dennowiggle/Retro-PETER/Hardware/PETER/output/PETER_V0_3d_Bottom.jpg

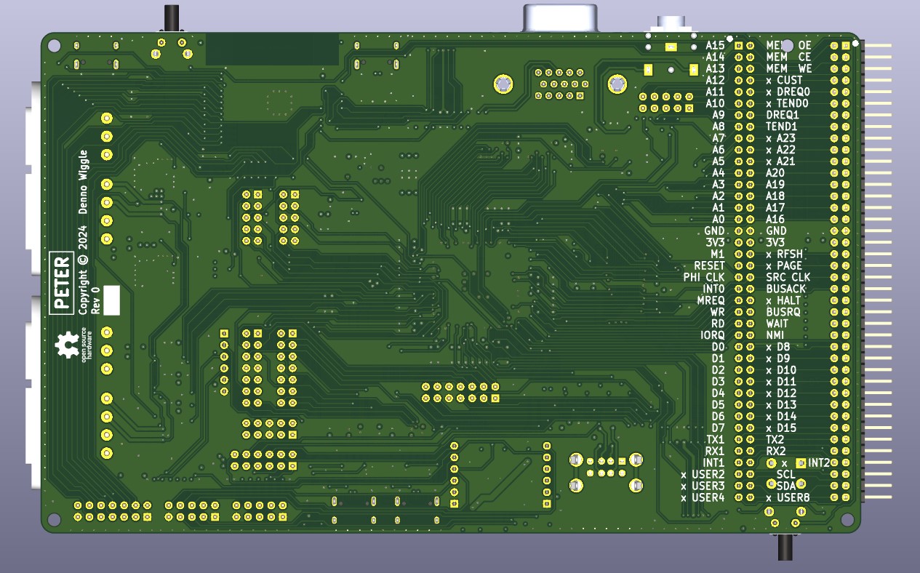
Hardware/PETER/output/PETER_V0_3d_Bottom.jpg
