dennowiggle/Retro-PETER/Hardware/PETER/output/PETER_V0_3d_Front.jpg

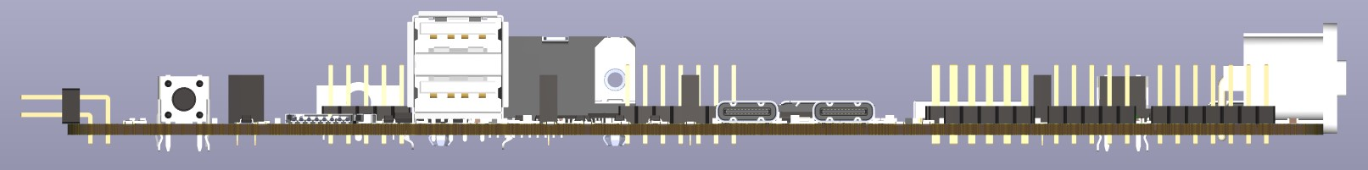
Hardware/PETER/output/PETER_V0_3d_Front.jpg
