dennowiggle/Retro-PETER/Hardware/PETER/output/PETER_V0_3d_Rear.jpg

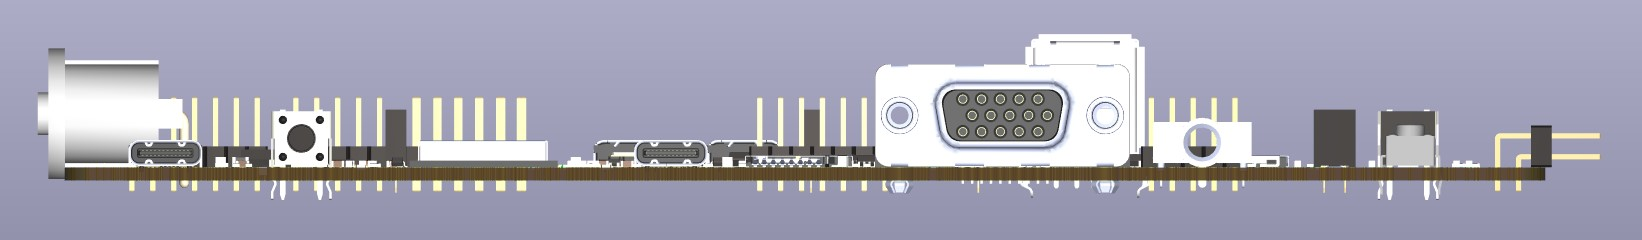
Hardware/PETER/output/PETER_V0_3d_Rear.jpg
