dennowiggle/Retro-PETER/Hardware/BALD/output/BALD_V0.0_BW.pdf

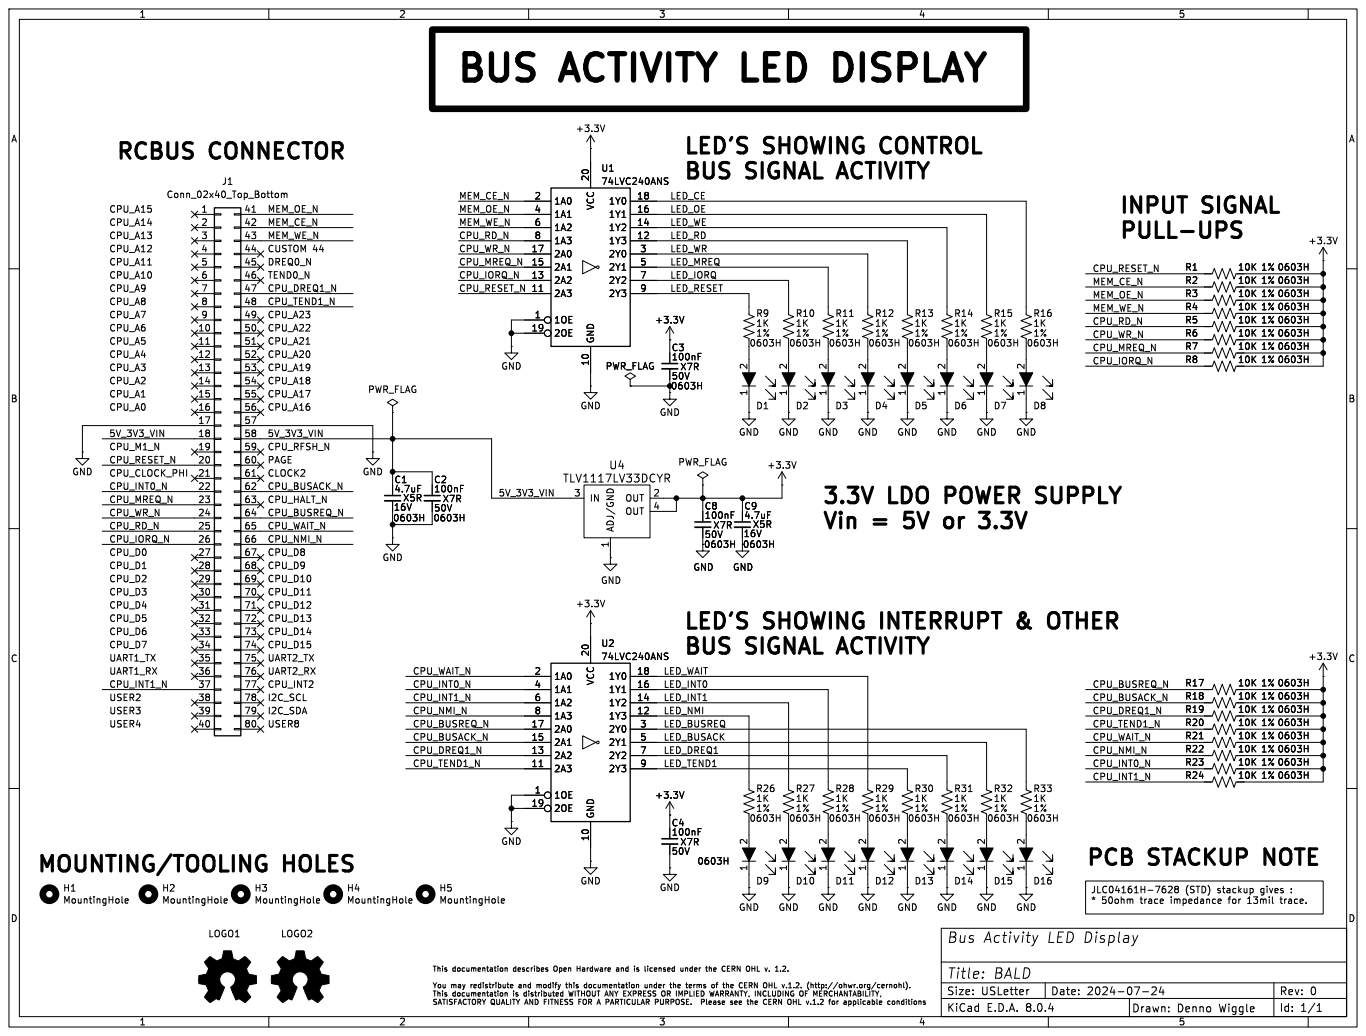
[picture p65: page 1]

Bus Activity LED Display
