dennowiggle/Retro-PETER/Hardware/BALD/output/BALD_V0.0_Color.pdf

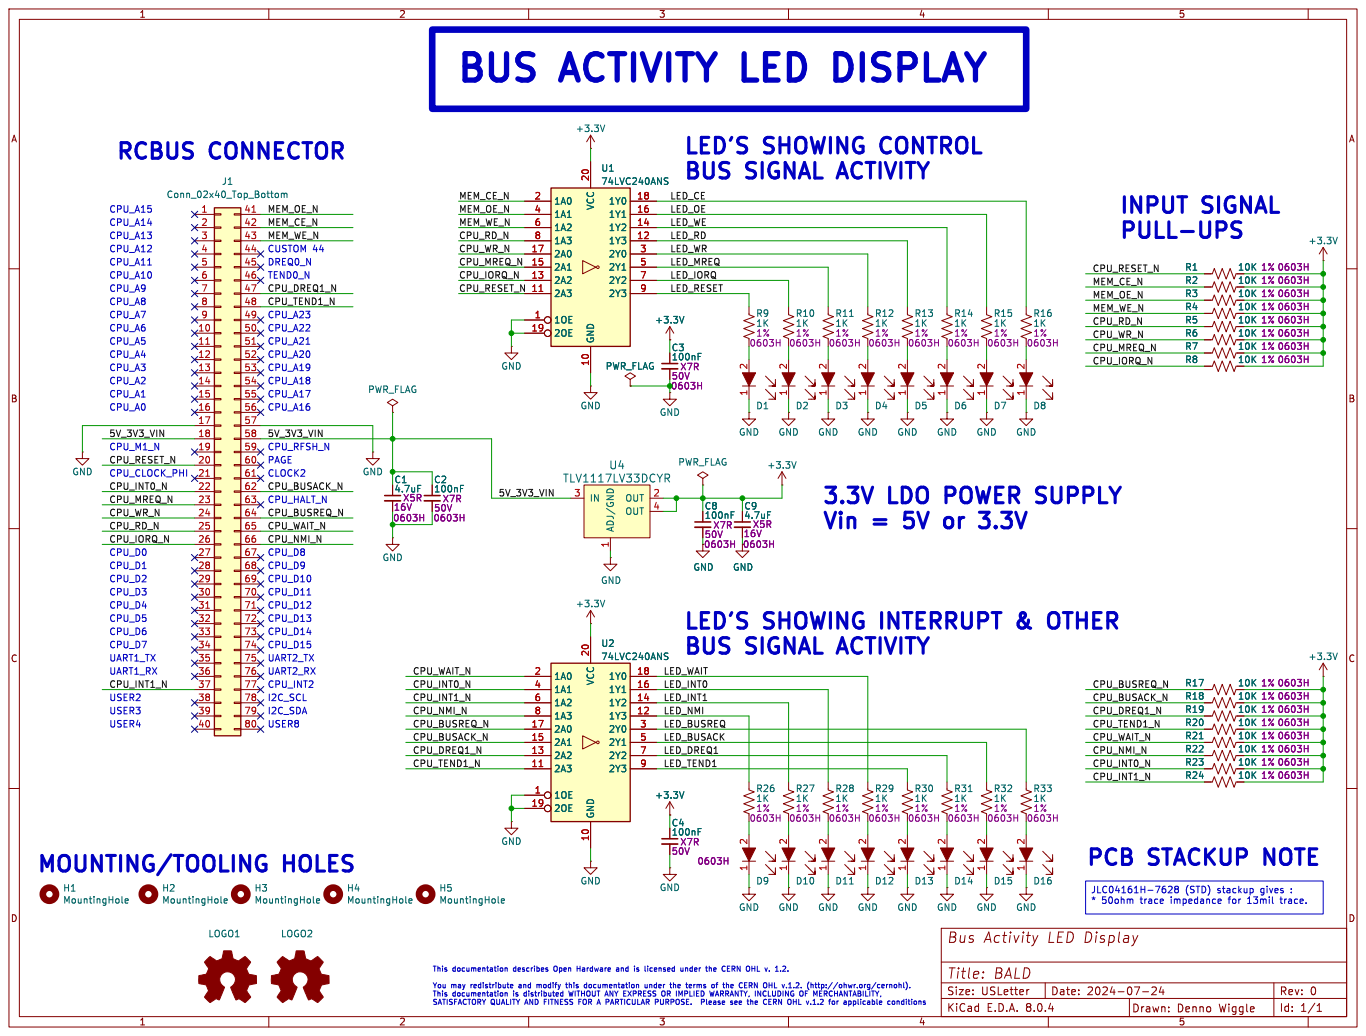
[picture p66: page 1]

Bus Activity LED Display
