dennowiggle/Retro-PETER/Hardware/GOLD/output/GOLD_V0.0_BW.pdf

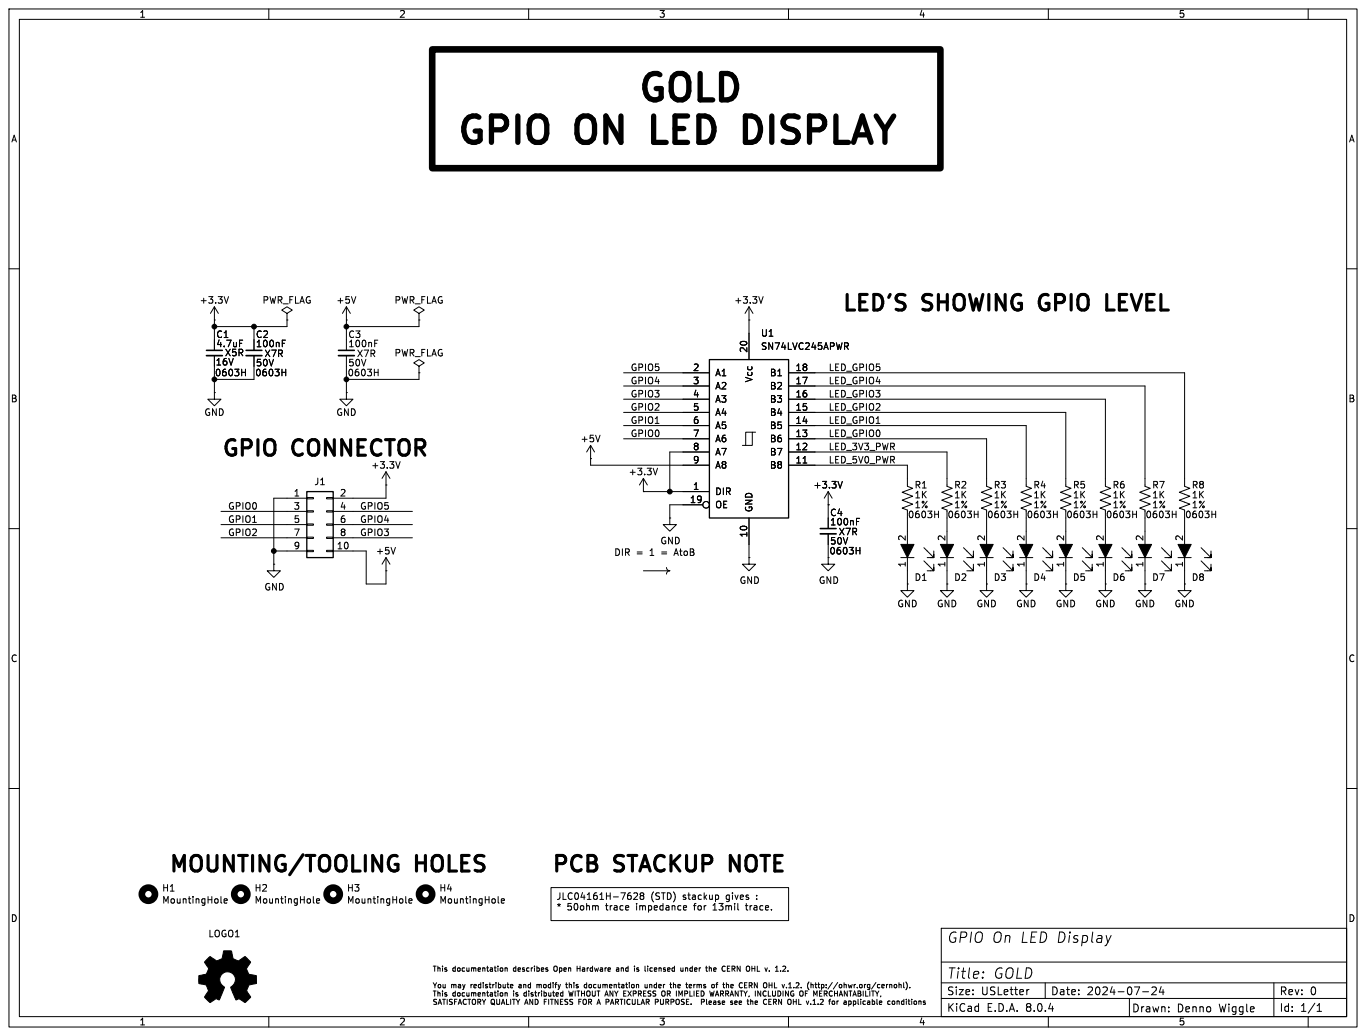
[picture p67: page 1]

GPIO ON LED DISPLAY

GPIO On LED Display
