dennowiggle/Retro-PETER/Hardware/GOLD/output/GOLD_V0.0_Color.pdf

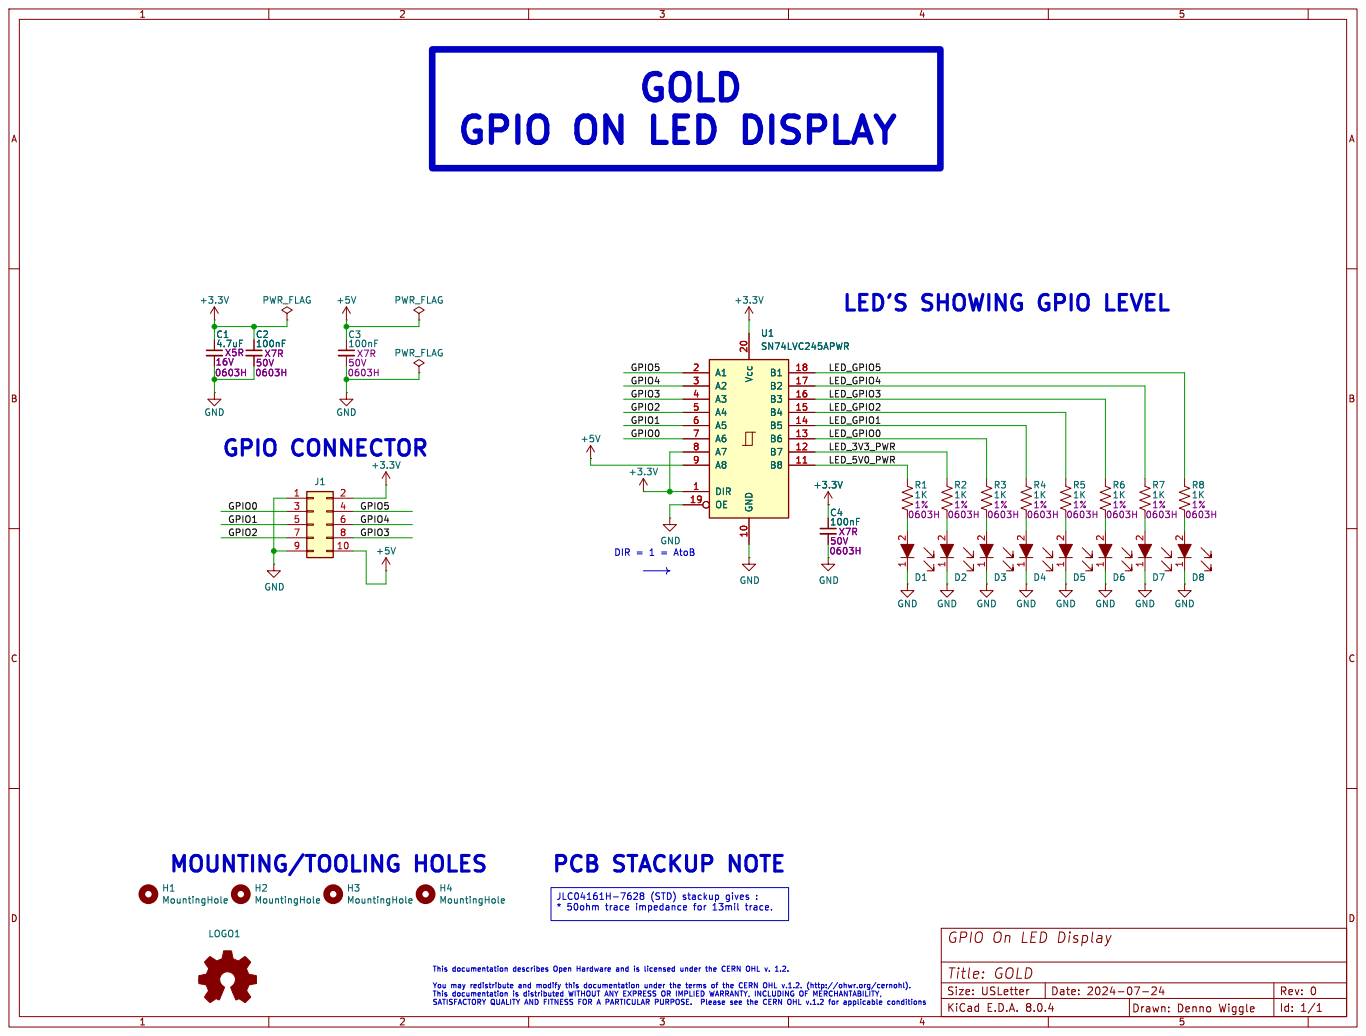
[picture p68: page 1]

GPIO ON LED DISPLAY

LED'S SHOWING GPIO LEVEL

GPIO On LED Display
