dennowiggle/Retro-PETER/Hardware/PETER/output/PETER_V0.0_Color.pdf

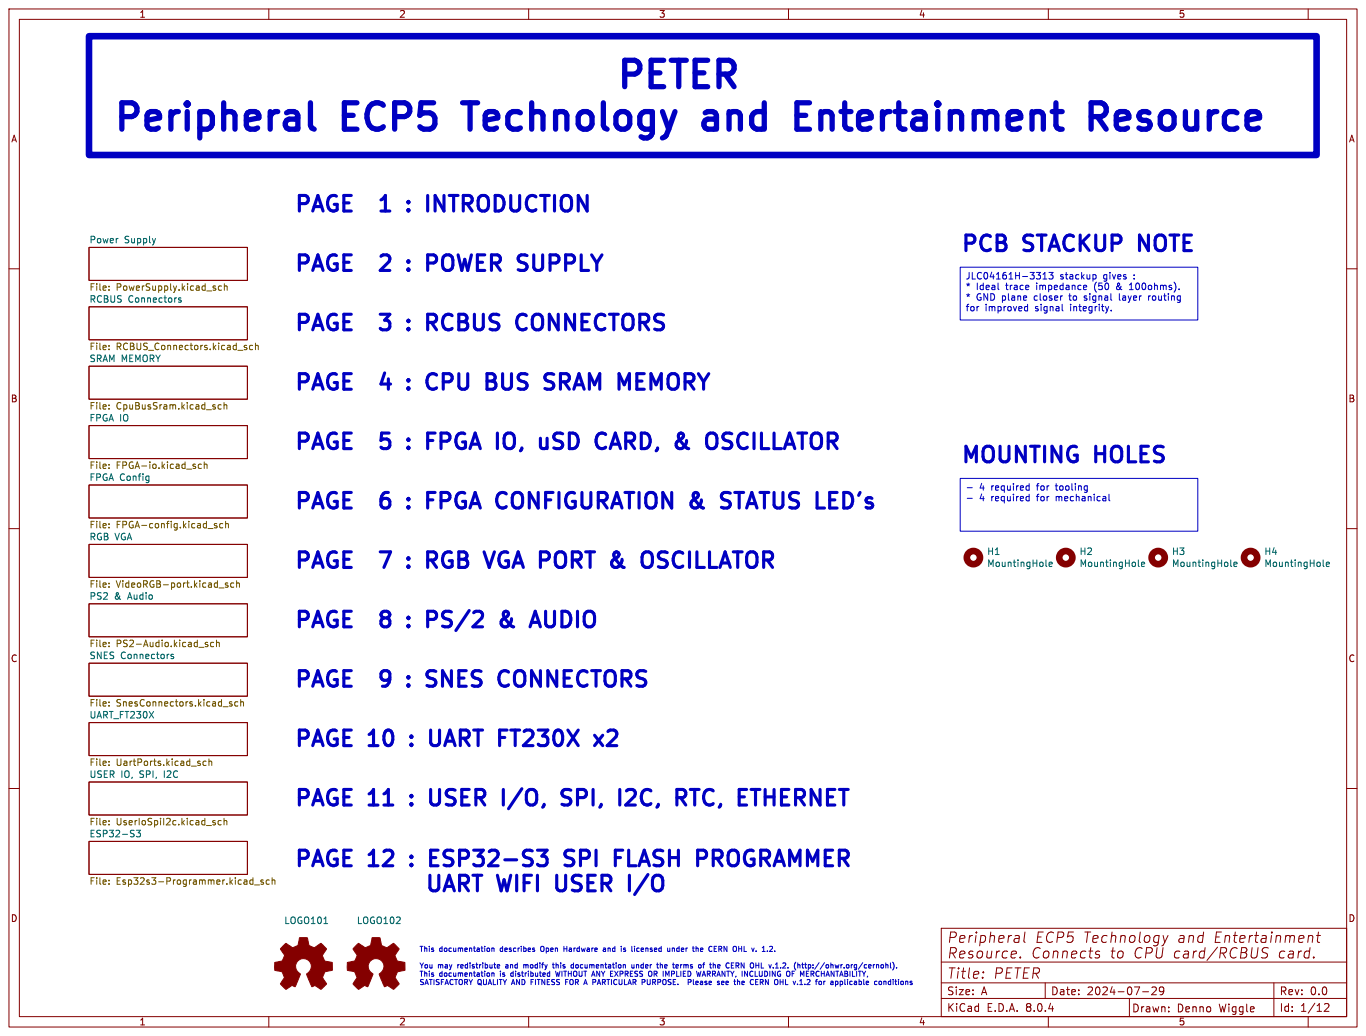
[picture p81: page 1]

Power Supply File: PowerSupply.kicad_sch SRAM MEMORY
File: FPGA-io.kicad_sch PS2 & Audio File: PS2-Audio.kicad_sch FPGA Config File: FPGA-config.kicad_sch SNES Connectors File: SnesConnectors.kicad_sch USER IO, SPI, I2C

RCBUS Connectors File: RCBUS_Connectors.kicad_sch FPGA IO

File: CpuBusSram.kicad_sch RGB VGA

File: UartPorts.kicad_sch ESP32-S3 File: Esp32s3-Programmer.kicad_sch

PAGE 11 : USER I/O, SPI, I2C, RTC, ETHERNET

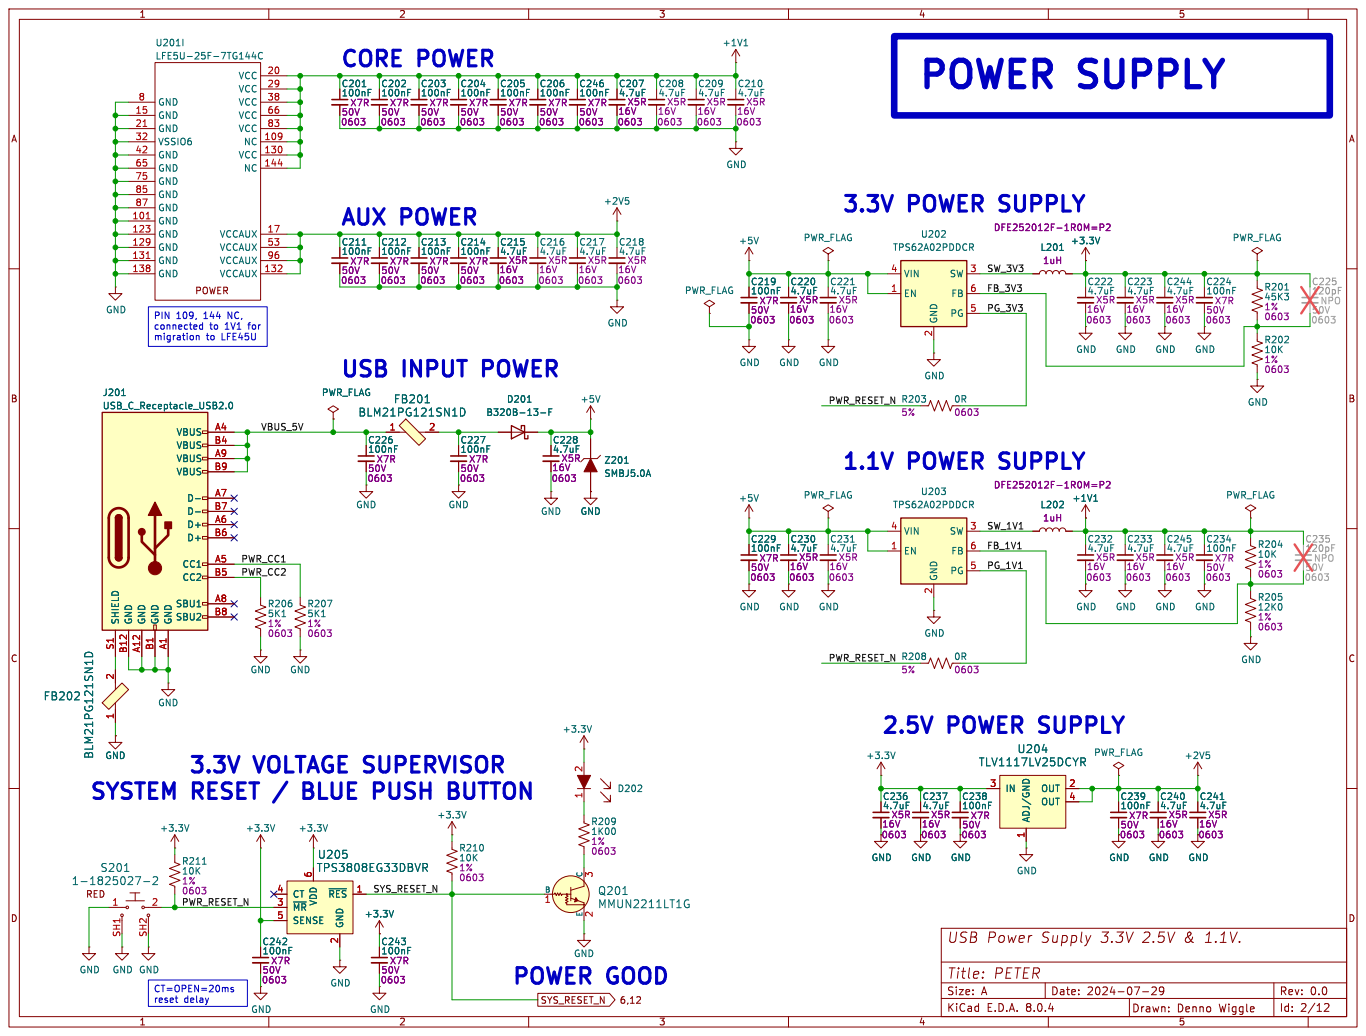
[picture p82: page 2]

2 SW 3 VIN 4 PG 5 FB 6 U202 TPS62A02PDDCR

2 SW 3 VIN 4 PG 5 FB 6 U203 TPS62A02PDDCR GND

1 2 D202 GND GND
SYSTEM RESET / BLUE PUSH BUTTON

2 ~{MR} 3 CT 4 SENSE 5 VDD

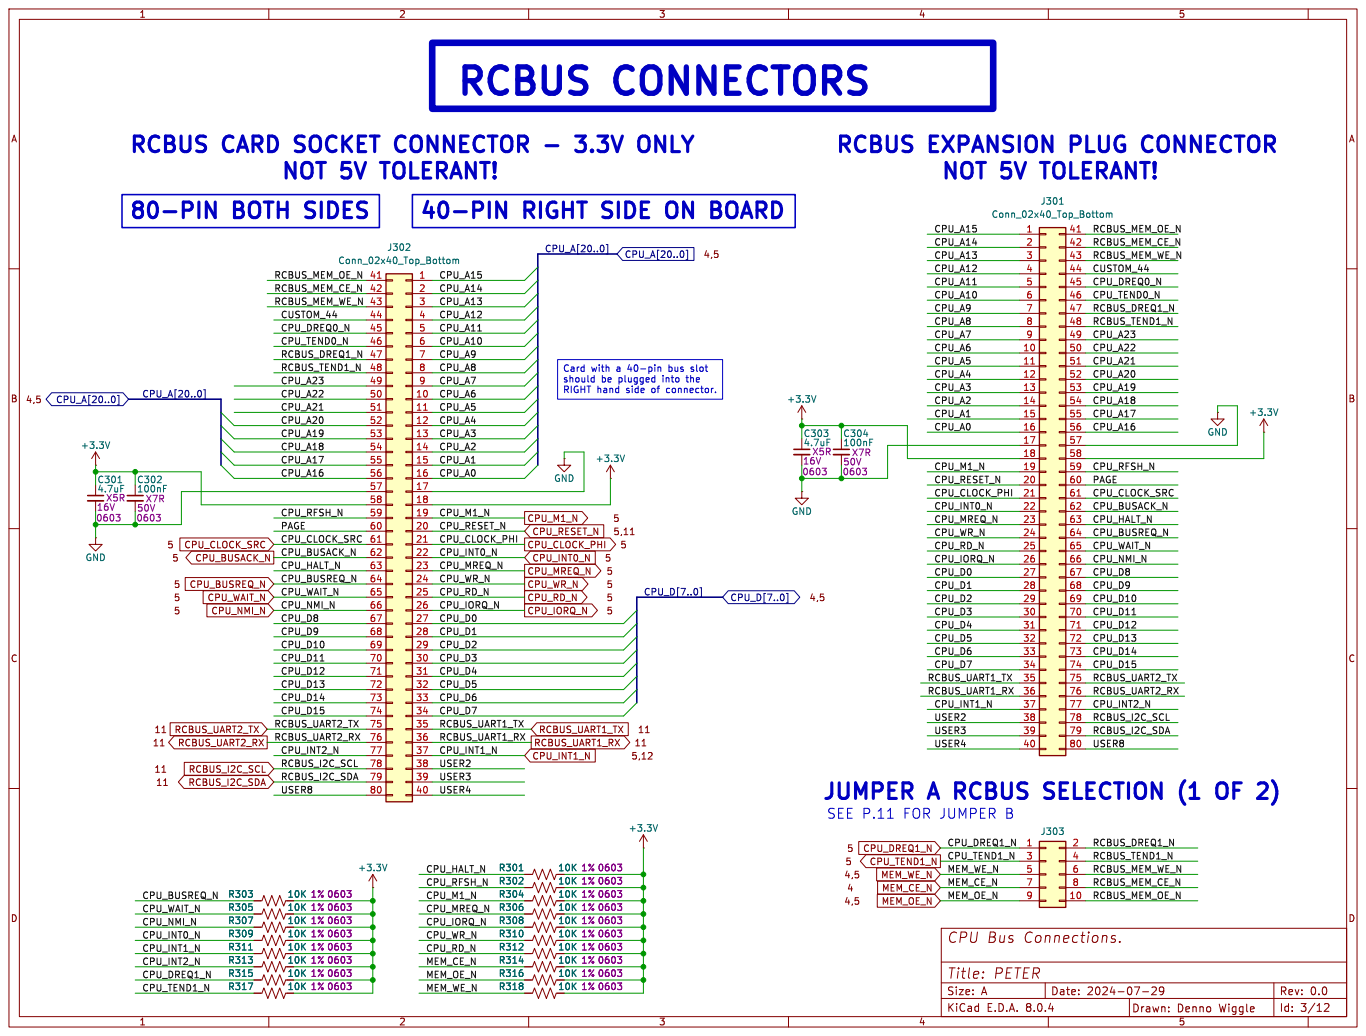
[picture p83: page 3]

RCBUS CARD SOCKET CONNECTOR - 3.3V ONLY

RCBUS EXPANSION PLUG CONNECTOR

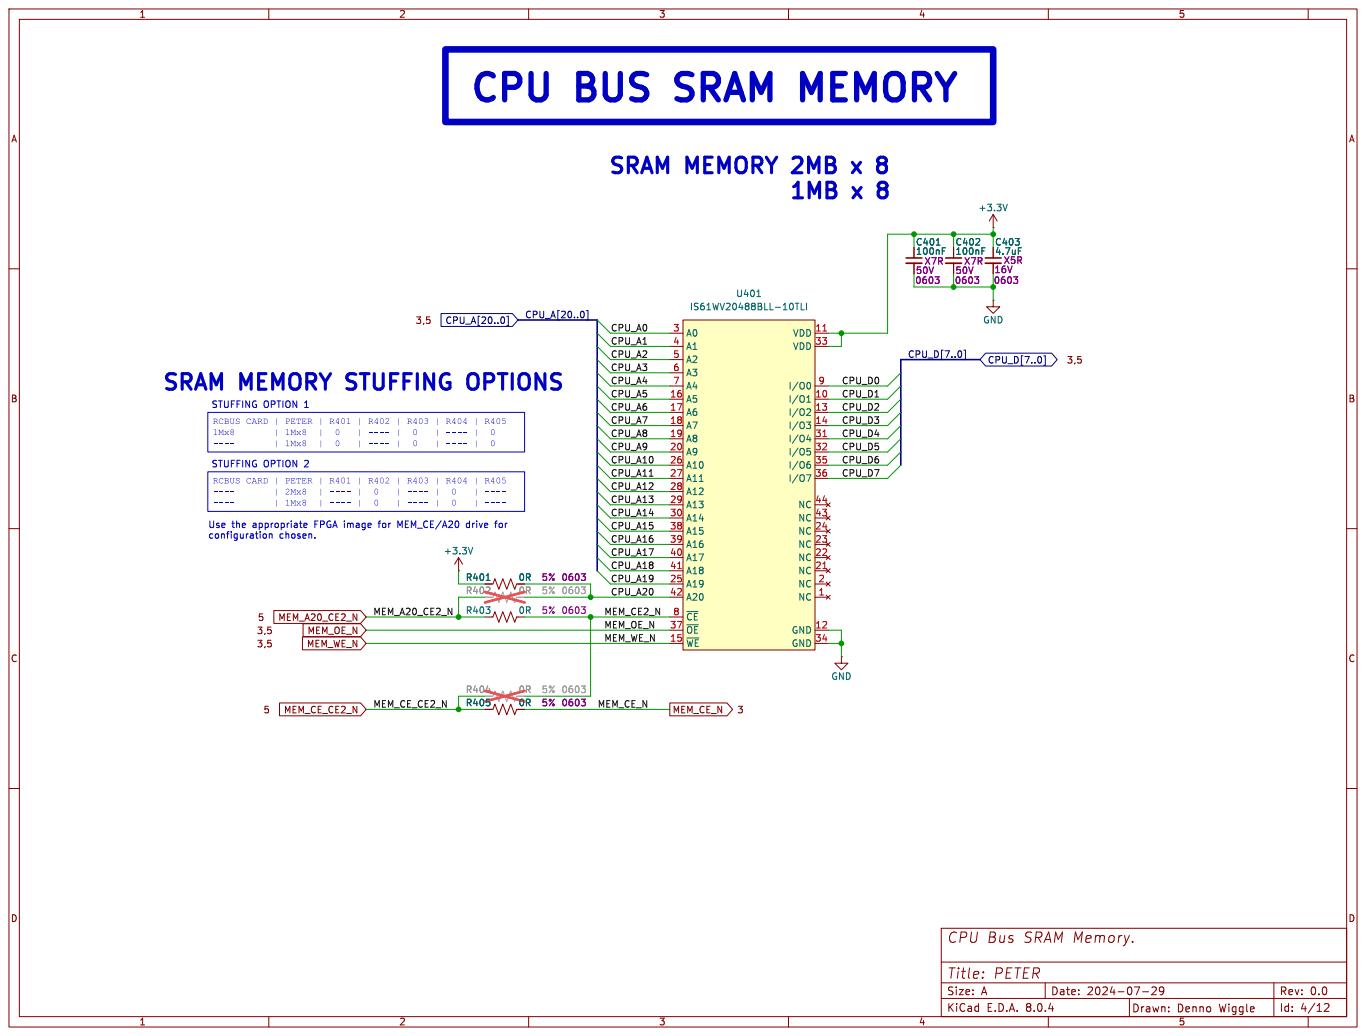
[picture p84: page 4]

CPU BUS SRAM MEMORY

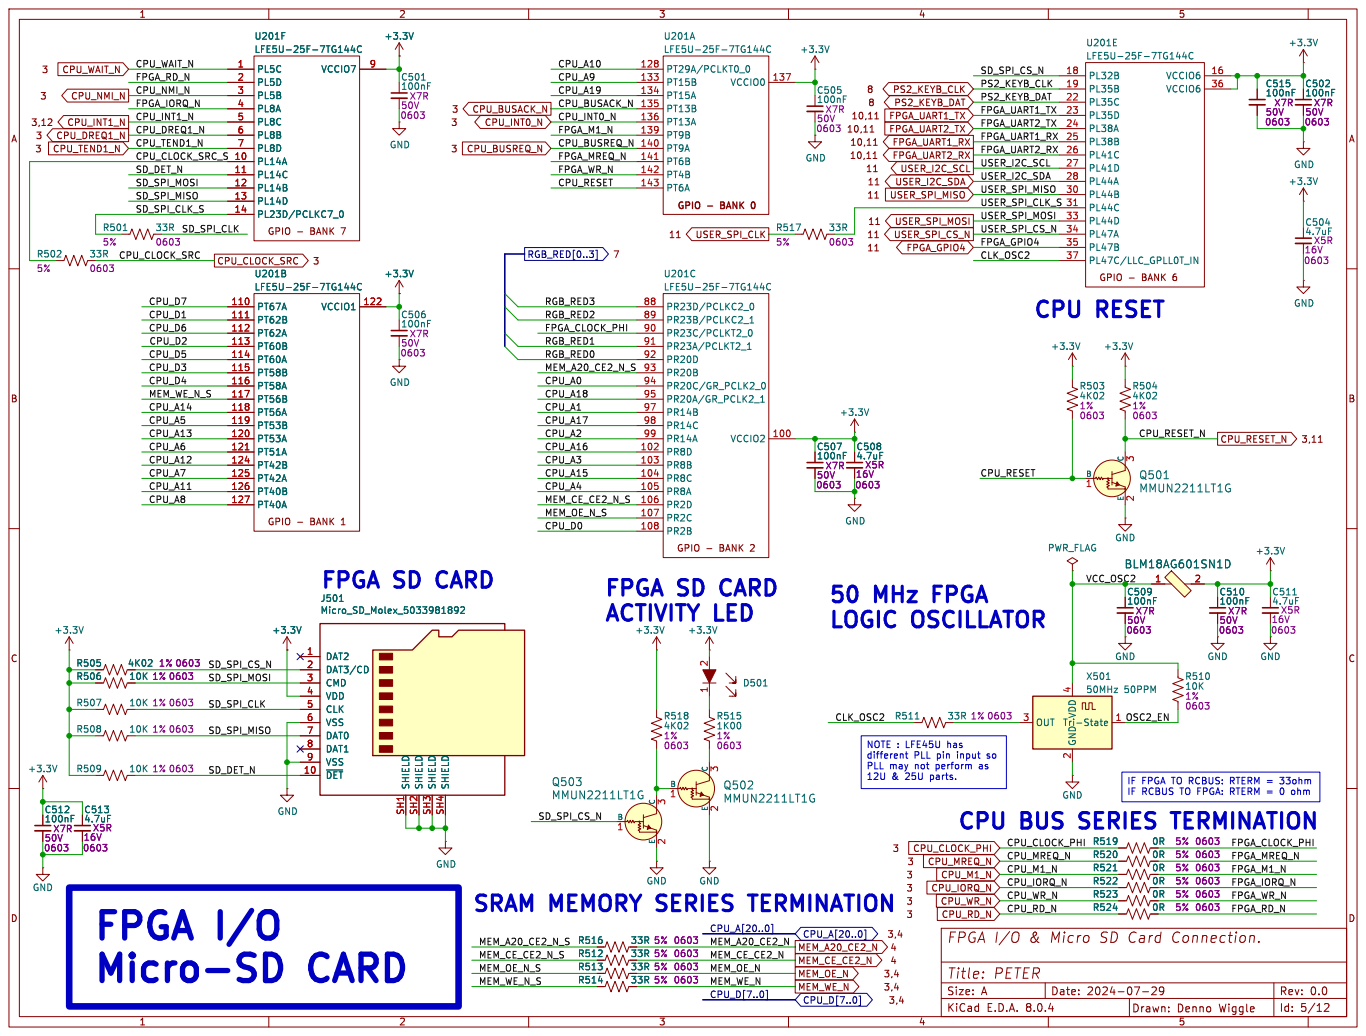
[picture p85: page 5]

IF FPGA TO RCBUS: RTERM = 33ohm

CPU BUS SERIES TERMINATION

GND
SRAM MEMORY SERIES TERMINATION

FPGA I/O & Micro SD Card Connection.

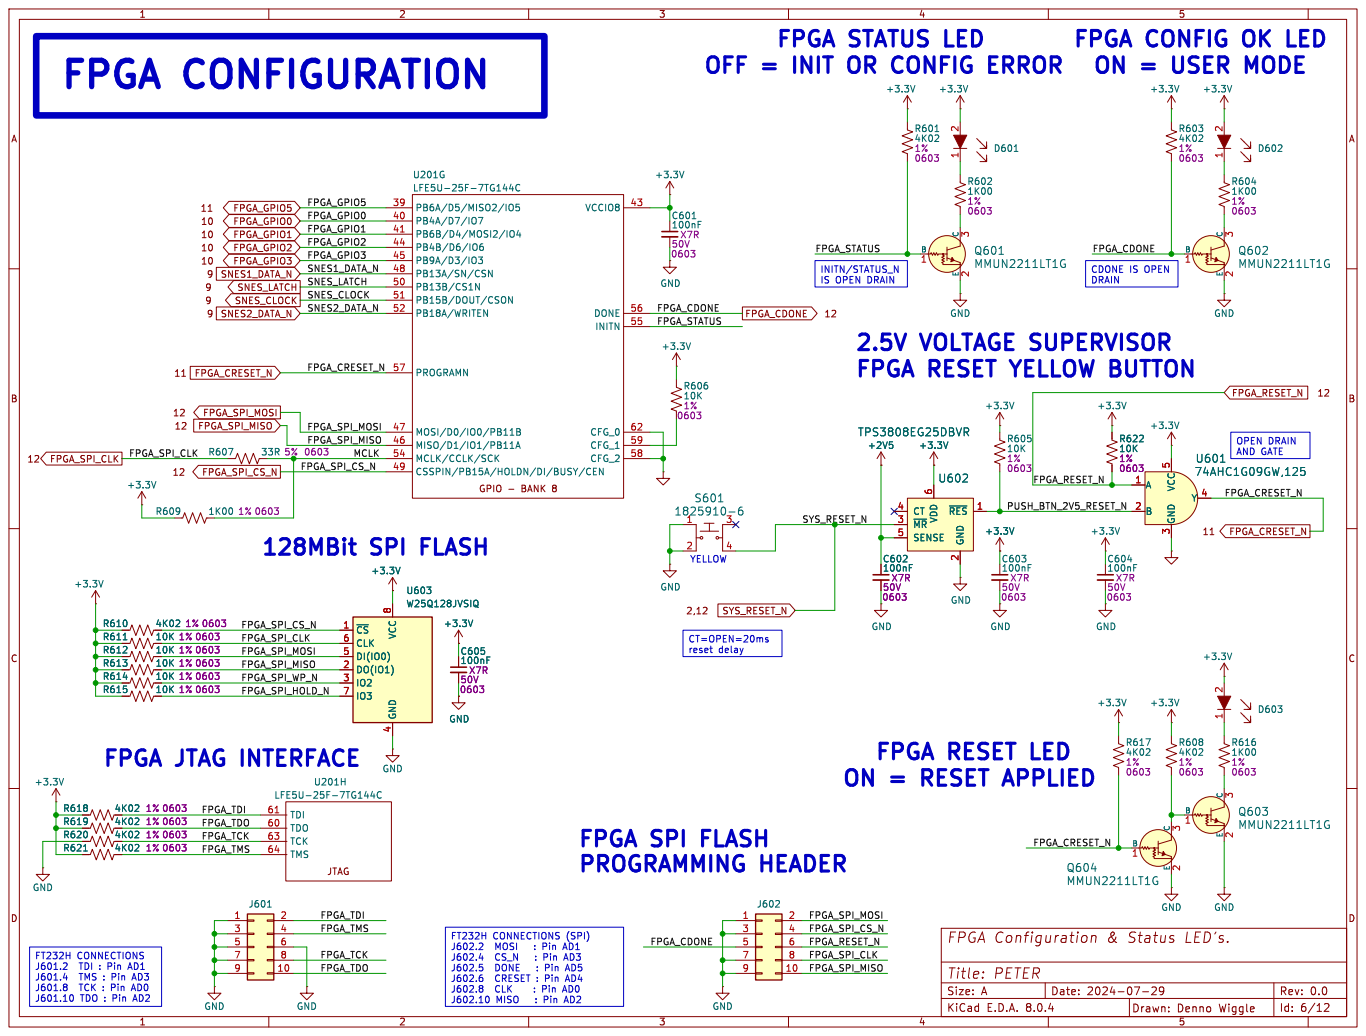
[picture p86: page 6]

FPGA STATUS LED
OFF = INIT OR CONFIG ERROR

AND GATE FPGA CONFIGURATION

2.5V VOLTAGE SUPERVISOR
FPGA RESET YELLOW BUTTON

2 ~{MR} 3 CT 4 SENSE 5 VDD

YELLOW FPGA SPI FLASH

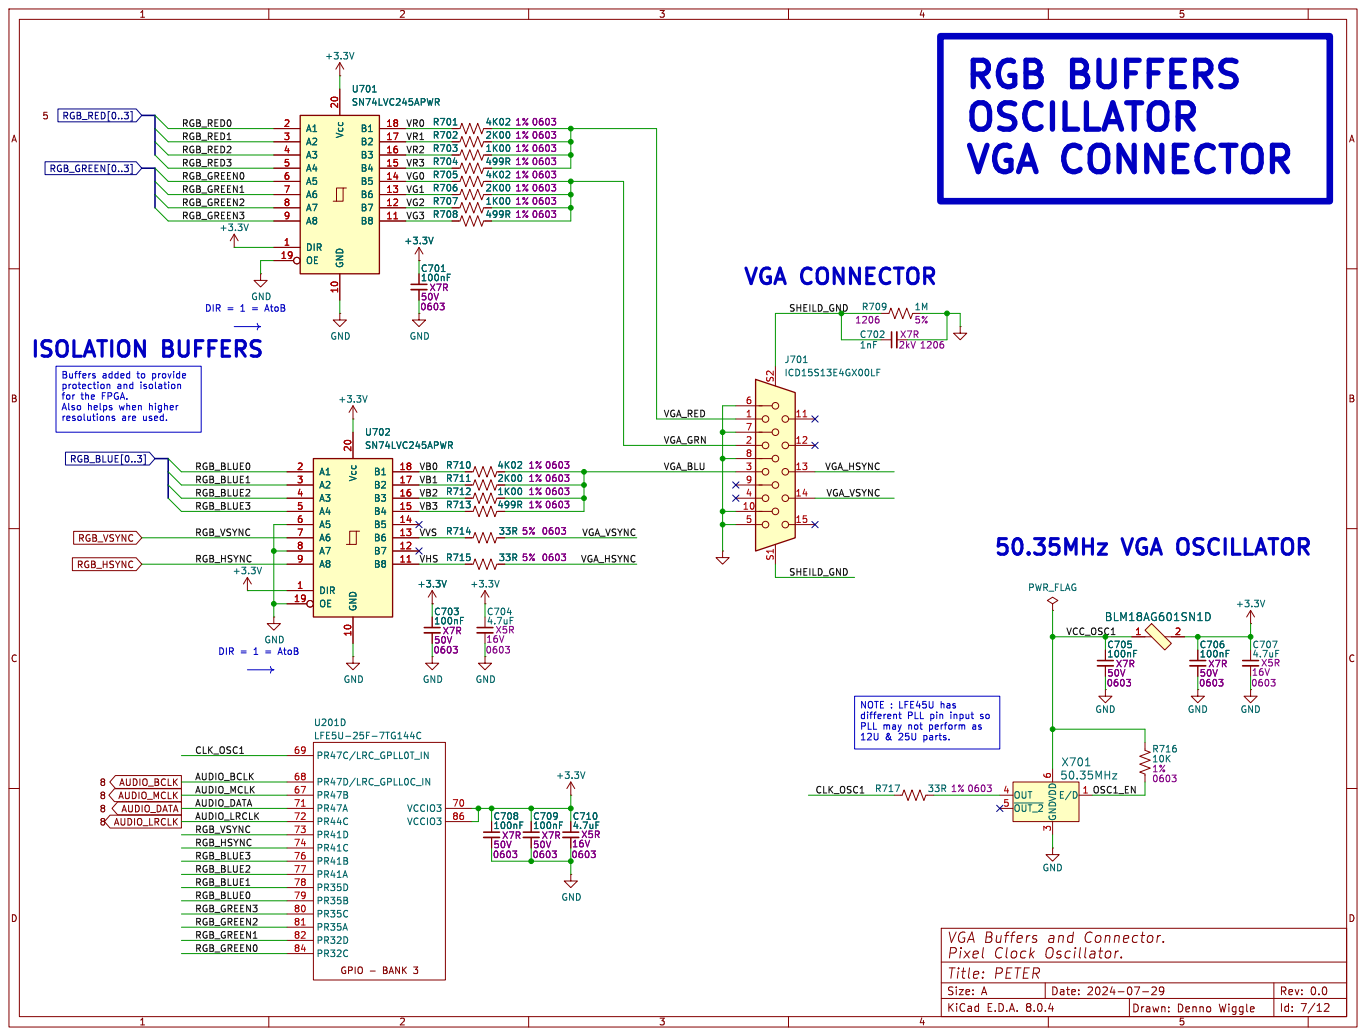
[picture p87: page 7]

Buffers added to provide
for the FPGA. Also helps when higher
8 AUDIO_LRCLK RGB_HSYNC

VGA Buffers and Connector.
Pixel Clock Oscillator.
Id: 7/12 Title: PETER

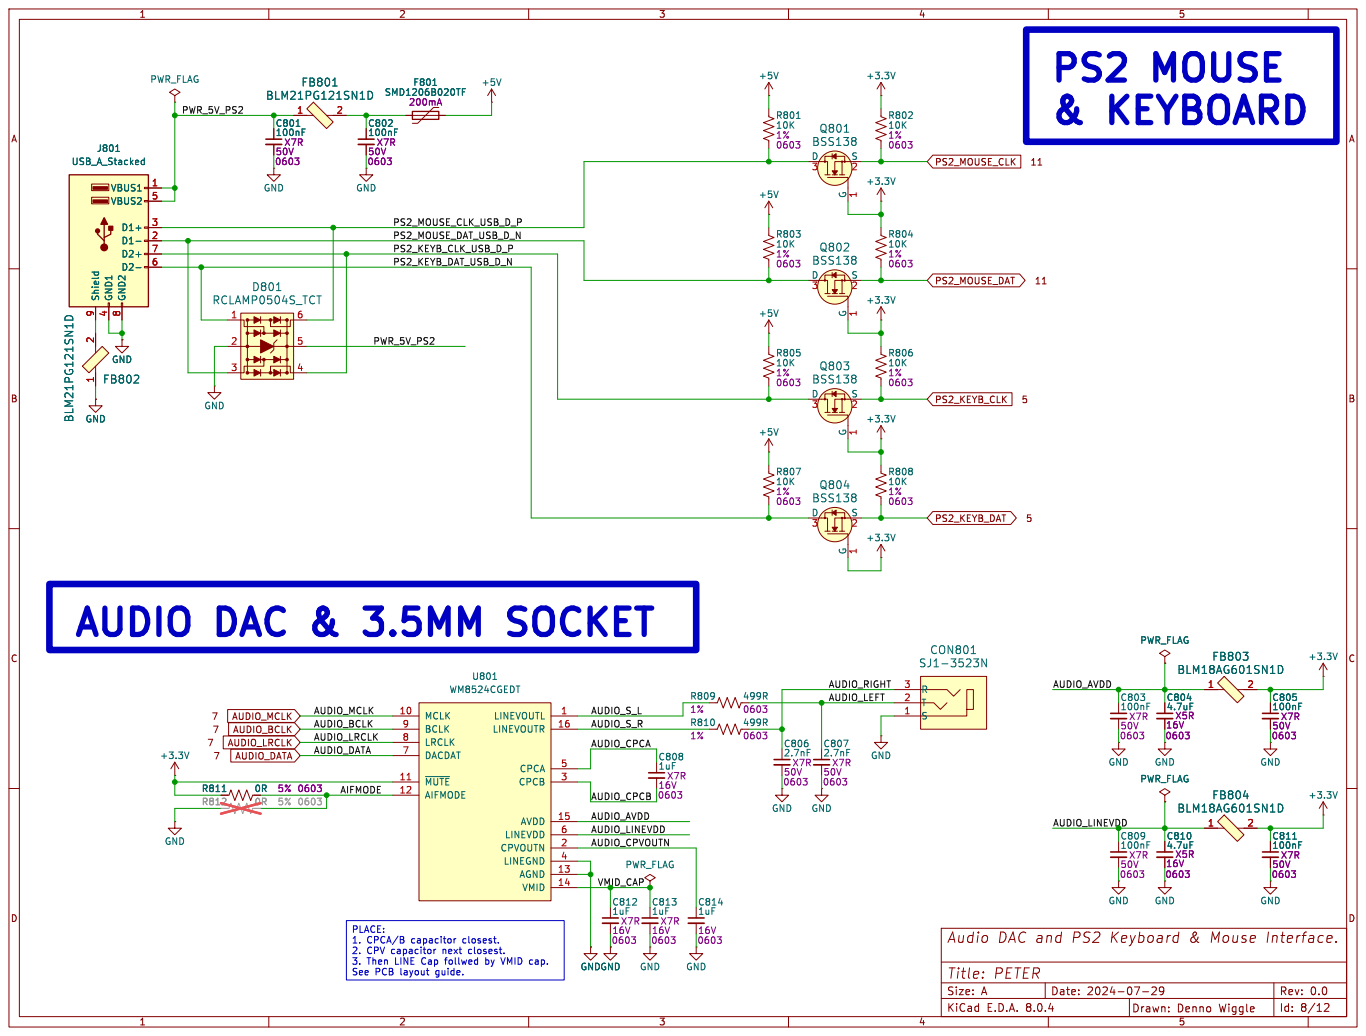
[picture p88: page 8]

Audio DAC and PS2 Keyboard & Mouse Interface.

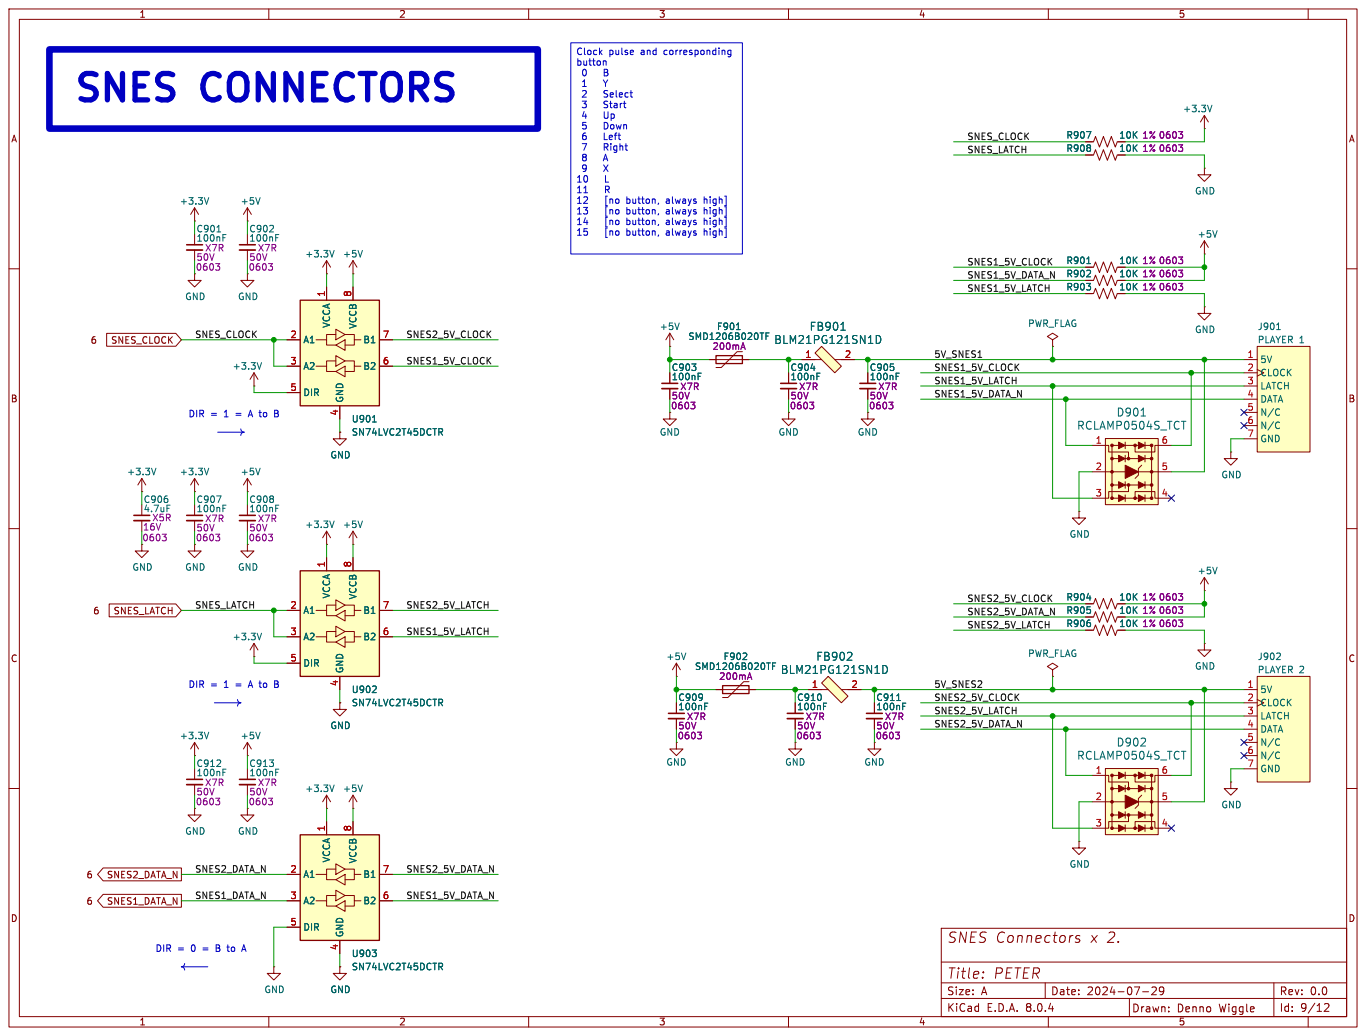
[picture p89: page 9]

Clock pulse and corresponding
button
DIR = 1 = A to B DIR = 1 = A to B DIR = 0 = B to A SNES CONNECTORS

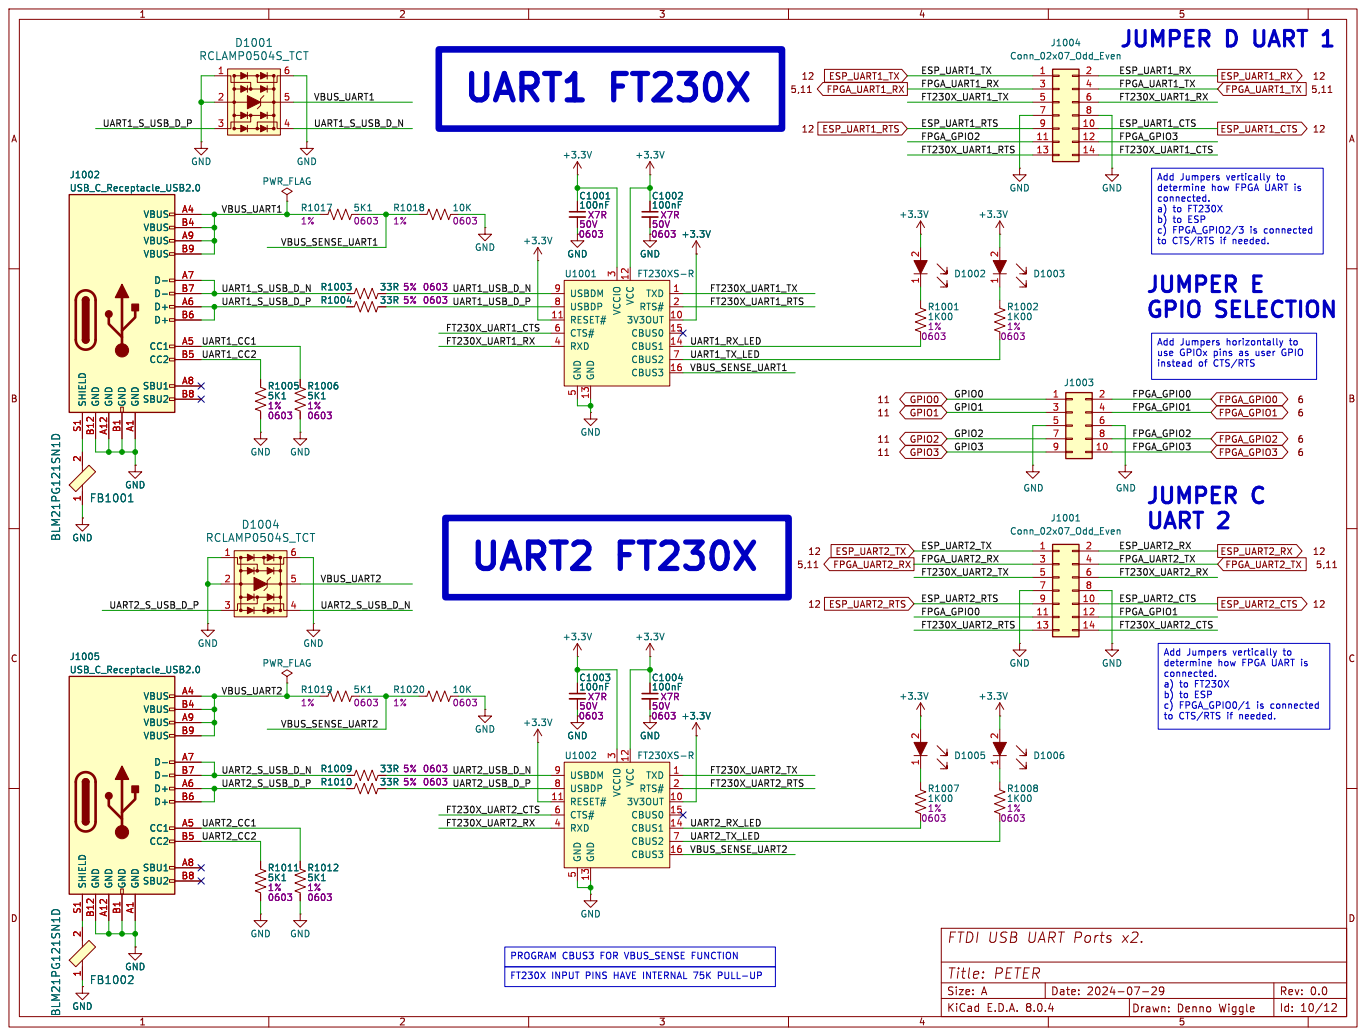
[picture p90: page 10]

use GPIOx pins as user GPIO

instead of CTS/RTS UART2 FT230X

1 2 FB1002 BLM21PG121SN1D GND A1 GND A12 VBUS A4 CC1 A5 D+ A6 D- A7 SBU1 A8 VBUS A9 GND B1 GND B12 VBUS B4 CC2 B5 D+ B6 D- B7 SBU2 B8 VBUS B9 SHIELD S1

b) to ESP
c) FPGA_GPIO0/1 is connected
to CTS/RTS if needed.

FTDI USB UART Ports x2. GND

PROGRAM CBUS3 FOR VBUS_SENSE FUNCTION
FT230X INPUT PINS HAVE INTERNAL 75K PULL-UP

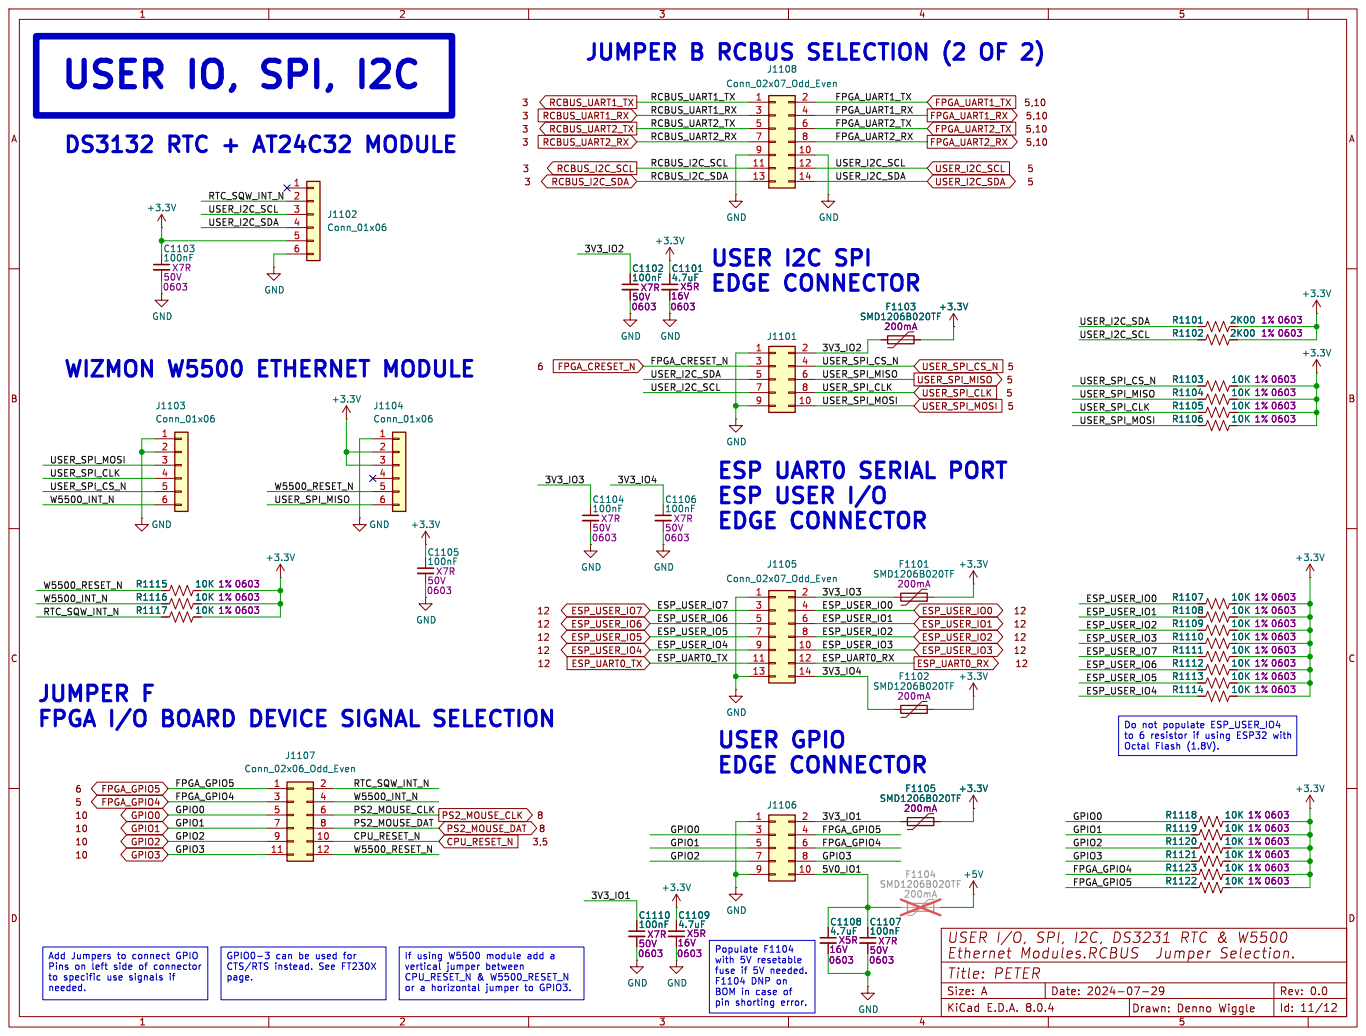
[picture p91: page 11]

JUMPER B RCBUS SELECTION (2 OF 2)

JUMPER F
FPGA I/O BOARD DEVICE SIGNAL SELECTION

If using W5500 module add a

Pins on left side of connector

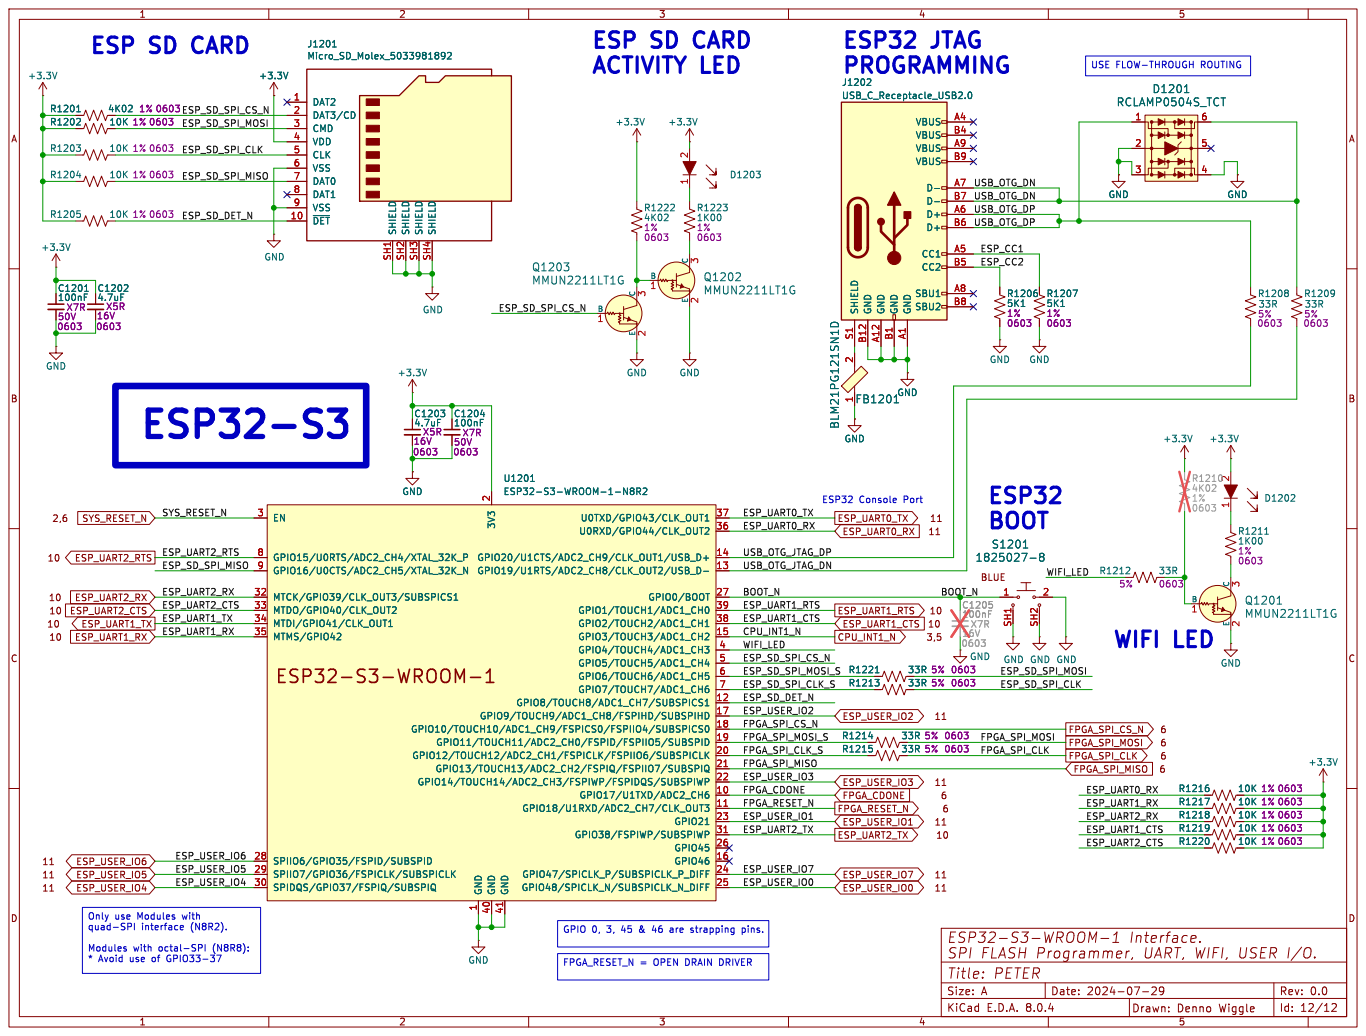
[picture p92: page 12]

USE FLOW-THROUGH ROUTING
6 D1201 RCLAMP0504S_TCT

2 GPIO12/TOUCH12/ADC2_CH1/FSPICLK/FSPIIO6/SUBSPICLK 20 GPIO13/TOUCH13/ADC2_CH2/FSPIQ/FSPIIO7/SUBSPIQ 21 GPIO14/TOUCH14/ADC2_CH3/FSPIWP/FSPIDQS/SUBSPIWP 22 GPIO21 23 GPIO47/SPICLK_P/SUBSPICLK_P_DIFF 24 GPIO48/SPICLK_N/SUBSPICLK_N_DIFF 25 GPIO45 26 GPIO0/BOOT 27 SPIIO6/GPIO35/FSPID/SUBSPID 28 SPIIO7/GPIO36/FSPICLK/SUBSPICLK 29 EN 3 SPIDQS/GPIO37/FSPIQ/SUBSPIQ 30 GPIO38/FSPIWP/SUBSPIWP 31 MTCK/GPIO39/CLK_OUT3/SUBSPICS1 32 MTDO/GPIO40/CLK_OUT2 33 MTDI/GPIO41/CLK_OUT1 34 MTMS/GPIO42 35 U0RXD/GPIO44/CLK_OUT2 36 U0TXD/GPIO43/CLK_OUT1 37 GPIO2/TOUCH2/ADC1_CH1 38 GPIO1/TOUCH1/ADC1_CH0 39 GPIO4/TOUCH4/ADC1_CH3 4 GPIO5/TOUCH5/ADC1_CH4 5 GPIO6/TOUCH6/ADC1_CH5 6 GPIO7/TOUCH7/ADC1_CH6 7 GPIO15/U0RTS/ADC2_CH4/XTAL_32K_P 8 GPIO16/U0CTS/ADC2_CH5/XTAL_32K_N 9 GND 40 GND 41 U1201 ESP32-S3-WROOM-1-N8R2 C1204

2 GPIO12/TOUCH12/ADC2_CH1/FSPICLK/FSPIIO6/SUBSPICLK 20 GPIO13/TOUCH13/ADC2_CH2/FSPIQ/FSPIIO7/SUBSPIQ 21 GPIO14/TOUCH14/ADC2_CH3/FSPIWP/FSPIDQS/SUBSPIWP 22 GPIO21 23 GPIO47/SPICLK_P/SUBSPICLK_P_DIFF 24 GPIO48/SPICLK_N/SUBSPICLK_N_DIFF 25 GPIO45 26 GPIO0/BOOT 27 SPIIO6/GPIO35/FSPID/SUBSPID 28 SPIIO7/GPIO36/FSPICLK/SUBSPICLK 29 EN 3 SPIDQS/GPIO37/FSPIQ/SUBSPIQ 30 GPIO38/FSPIWP/SUBSPIWP 31 MTCK/GPIO39/CLK_OUT3/SUBSPICS1 32 MTDO/GPIO40/CLK_OUT2 33 MTDI/GPIO41/CLK_OUT1 34 MTMS/GPIO42 35 U0RXD/GPIO44/CLK_OUT2 36 U0TXD/GPIO43/CLK_OUT1 37 GPIO2/TOUCH2/ADC1_CH1 38 GPIO1/TOUCH1/ADC1_CH0 39 GPIO4/TOUCH4/ADC1_CH3 4 GPIO5/TOUCH5/ADC1_CH4 5 GPIO6/TOUCH6/ADC1_CH5 6 GPIO7/TOUCH7/ADC1_CH6 7 GPIO15/U0RTS/ADC2_CH4/XTAL_32K_P 8 GPIO16/U0CTS/ADC2_CH5/XTAL_32K_N 9 GND 40 GND 41 C1204

1 GPIO17/U1TXD/ADC2_CH6 10 GPIO18/U1RXD/ADC2_CH7/CLK_OUT3 11 GPIO8/TOUCH8/ADC1_CH7/SUBSPICS1 12 GPIO19/U1RTS/ADC2_CH8/CLK_OUT2/USB_D- 13 GPIO20/U1CTS/ADC2_CH9/CLK_OUT1/USB_D+ 14 GPIO3/TOUCH3/ADC1_CH2 15 GPIO46 16 GPIO9/TOUCH9/ADC1_CH8/FSPIHD/SUBSPIHD 17 GPIO10/TOUCH10/ADC1_CH9/FSPICS0/FSPIIO4/SUBSPICS0 18 GPIO11/TOUCH11/ADC2_CH0/FSPID/FSPIIO5/SUBSPID 19 3V3

Only use Modules with
